dczia/Defcon31-Badge/Hardware/Final/3d/Cherry MX Keycap.SLDPRT

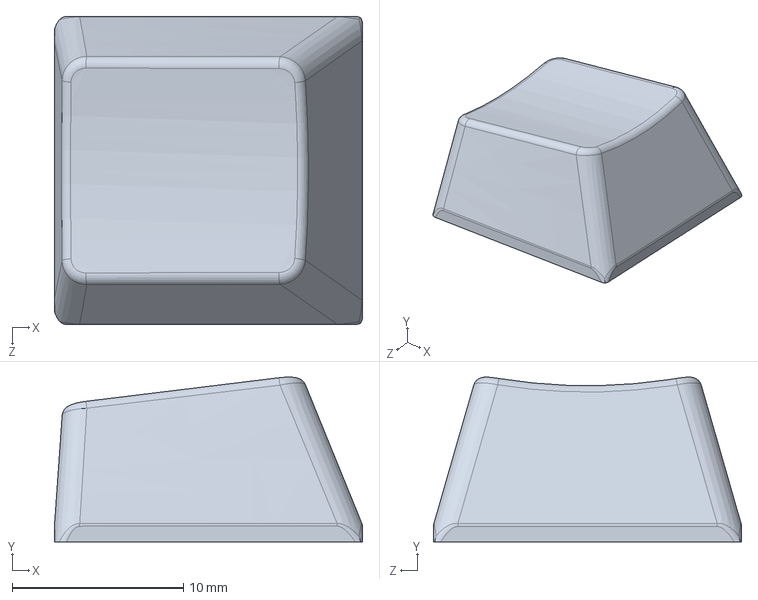
[picture p16: CAD file, 2023-07-15]
Hardware/Final/3d/Cherry MX Keycap.SLDPRT
18.0 x 9.64 x 18.0 mm
