dczia/Defcon31-Badge/Hardware/Final/3d/MicroSD.STEP

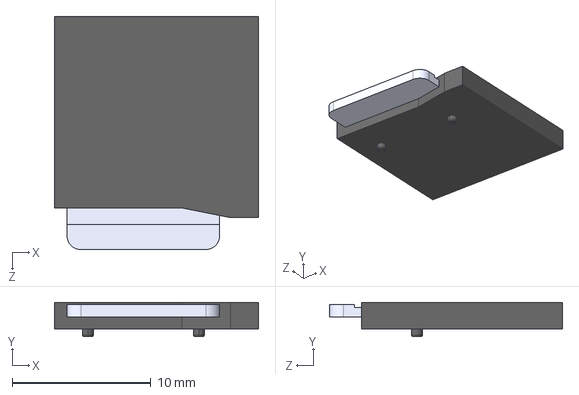
[picture p17: CAD file, 2023-07-14]
Hardware/Final/3d/MicroSD.STEP
14.7 x 2.45 x 16.8 mm
