dczia/Defcon31-Badge/Hardware/Final/3d/12mm Incremental Encoder - BOURNS PEC11S.stp

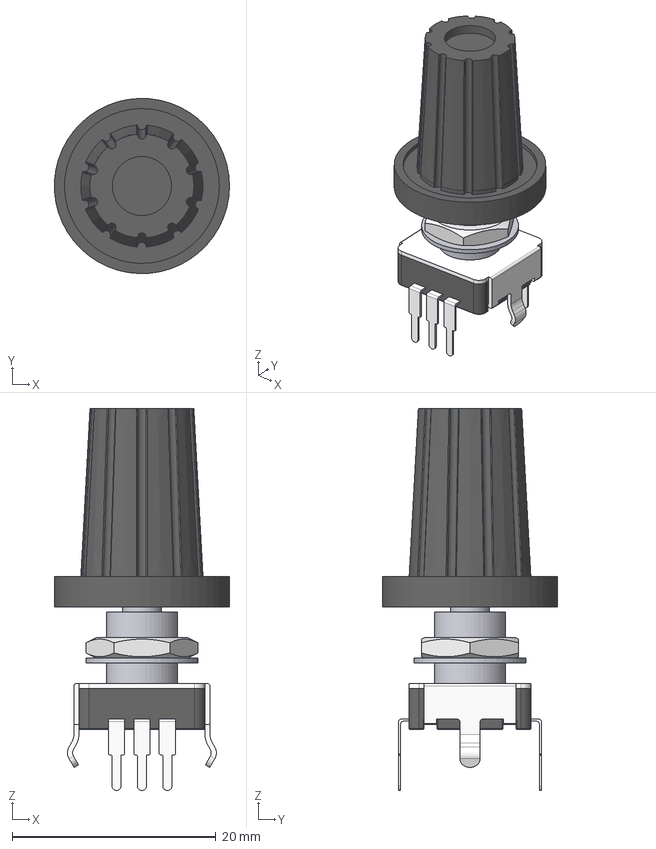
[picture p18: CAD file, 2023-07-11]
Hardware/Final/3d/12mm Incremental Encoder - BOURNS PEC11S.stp
17.2 x 17.2 x 37.5 mm
12mm Incremental Encoder Base
12mm Incremental Encoder Pin x 5
12mm Incremental Encoder Anti-Rotation Plate
12mm Incremental Encoder Threaded Tube
12mm Incremental Encoder Washer
M7x0.75 Hex Nut
12mm Incremental Encoder Shaft
12mm Incremental Encoder Cap
