dczia/Defcon31-Badge/Hardware/Final/3d/12mm Incremental Encoder - BOURNS PEC11S - No Knob.STEP

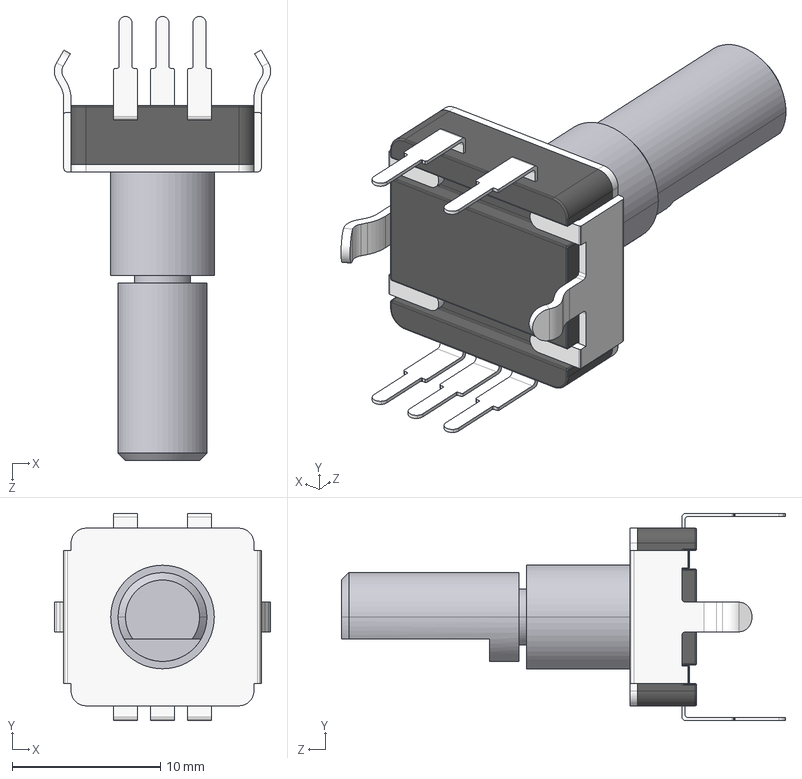
[picture p19: CAD file, 2023-07-11]
Hardware/Final/3d/12mm Incremental Encoder - BOURNS PEC11S - No Knob.STEP
14.6 x 14.0 x 30.0 mm
12mm Incremental Encoder Base.stp
12mm Incremental Encoder Pin.stp x 5
12mm Incremental Encoder Anti-Rotation Plate.stp
12mm Incremental Encoder Threaded Tube.stp
12mm Incremental Encoder Shaft.stp
