dczia/Defcon31-Badge/Hardware/Final/3d/MX.STEP

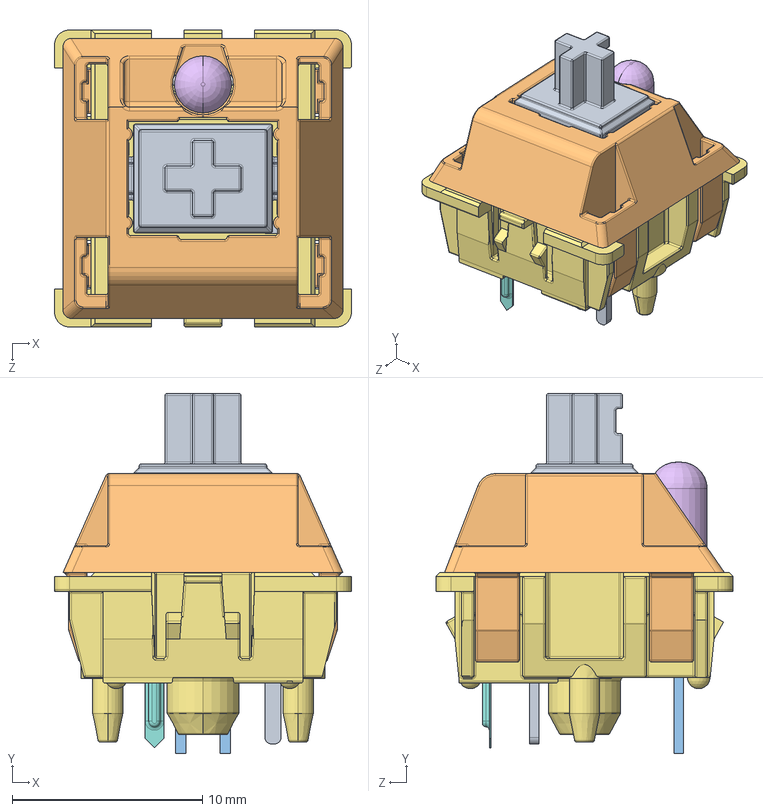
[picture p20: CAD file, 2023-07-11]
Hardware/Final/3d/MX.STEP
15.6 x 18.9 x 15.6 mm
MX ? ?? x 2
MX? ??LED
MX? ?? ??___
??___
