dczia/Defcon31-Badge/Hardware/Final/3d/Speaker-24x15.STEP

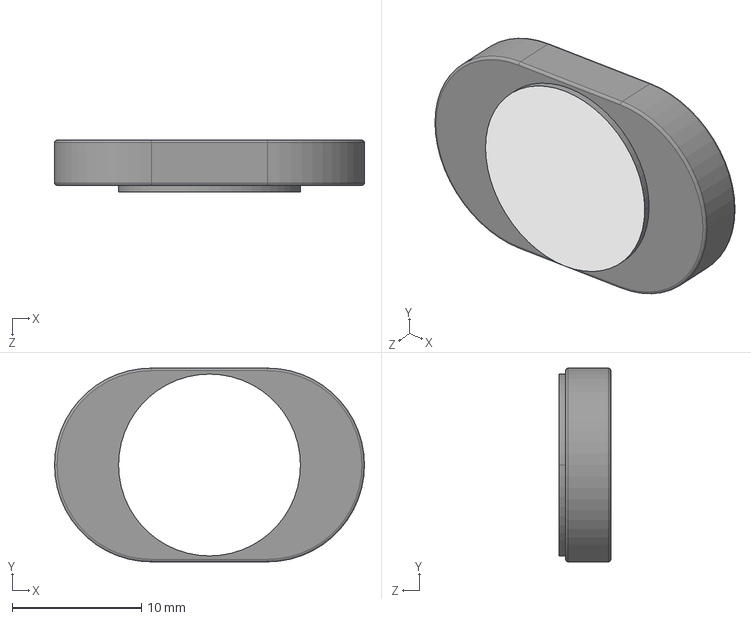
[picture p21: CAD file, 2023-07-11]
Hardware/Final/3d/Speaker-24x15.STEP
24.0 x 15.0 x 4.00 mm
