dczia/Defcon31-Badge/Software/Production/State.py

class State(object):
    def __init__(self):
        pass

    @property
    def name(self):
        return ""

    def enter(self, machine):
        pass

    def exit(self, machine):
        pass

    def update(self, machine):
        return True
